CircleTect/space-case/02_3D PRINT FILES/OPTIONAL_X2_CABLE_COMB_V2_BLU.3mf

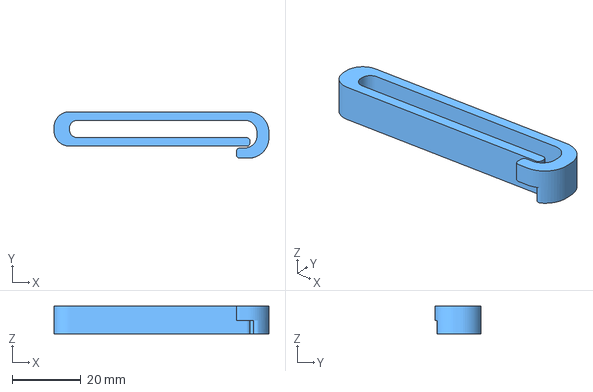
[picture p18: CAD file, 2022-10-08]
02_3D PRINT FILES/OPTIONAL_X2_CABLE_COMB_V2_BLU.3mf
62.5 x 13.5 x 8.00 mm
