CircleTect/space-case/02_3D PRINT FILES/OPTIONAL_X2_RAD_BRACKET_V1_BLK.3mf

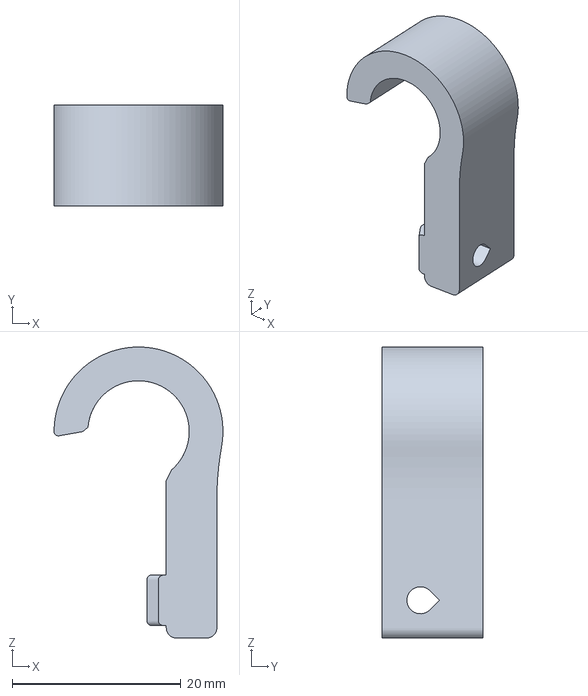
[picture p19: CAD file, 2022-10-08]
02_3D PRINT FILES/OPTIONAL_X2_RAD_BRACKET_V1_BLK.3mf
20.0 x 12.0 x 34.5 mm
