CircleTect/space-case/02_3D PRINT FILES/07_X2_MOBO_BRACKET_SHORT_V3_BLK.3mf

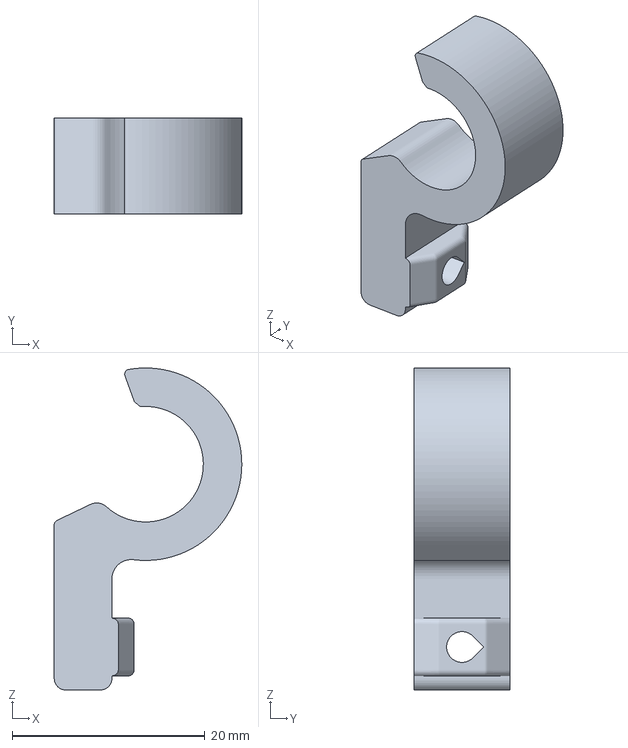
[picture p20: CAD file, 2022-10-08]
02_3D PRINT FILES/07_X2_MOBO_BRACKET_SHORT_V3_BLK.3mf
19.5 x 10.00 x 33.5 mm
