CircleTect/space-case/02_3D PRINT FILES/OPTIONAL_X2_3.5_DRIVE_SUPPORT_V4_BLK.3mf

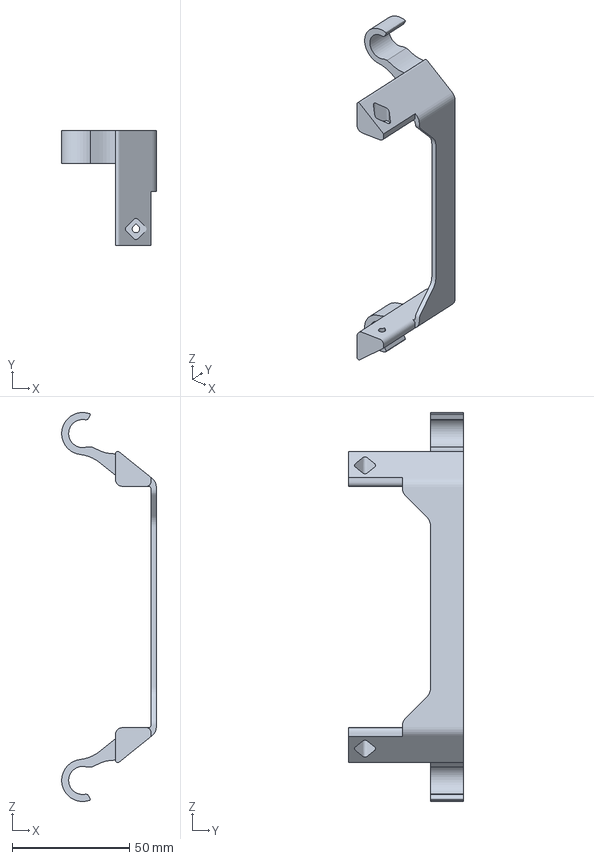
[picture p21: CAD file, 2022-10-08]
02_3D PRINT FILES/OPTIONAL_X2_3.5_DRIVE_SUPPORT_V4_BLK.3mf
40.4 x 49.0 x 166.1 mm
