CircleTect/space-case/02_3D PRINT FILES/05_X4_FOOT_V2_BLK.3mf

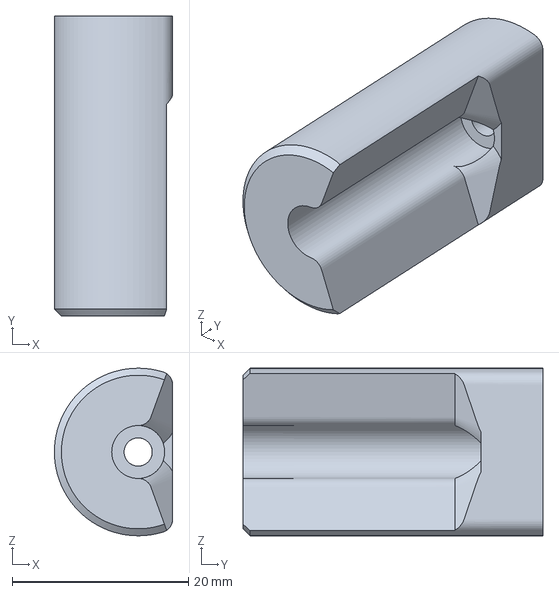
[picture p22: CAD file, 2022-10-08]
02_3D PRINT FILES/05_X4_FOOT_V2_BLK.3mf
13.4 x 34.0 x 19.0 mm
